laurencecrew/elead_dash/src/bitmaps.h

#ifndef BITMAPS_H
#define BITMAPS_H

#include <Arduino.h>

/*
	Bitmaps generated with http://javl.github.io/image2cpp/
*/

// 'icon_batt1', 6x11px
const unsigned char bm_icon_batt1 [] PROGMEM = {
	0x78, 0xfc, 0xfc, 0xcc, 0x8c, 0xcc, 0xcc, 0xcc, 0xcc, 0xfc, 0xfc
};
/* 'icon_batt2', 6x11px
const unsigned char bm_icon_batt2 [] PROGMEM = {
	0x78, 0xfc, 0xfc, 0x84, 0xb4, 0xe4, 0xcc, 0x9c, 0x84, 0xfc, 0xfc
};*/
// 'icon_motor', 6x11px
const unsigned char bm_icon_motor [] PROGMEM = {
	0x30, 0x30, 0x78, 0xfc, 0x00, 0xfc, 0xfc, 0xfc, 0xfc, 0xfc, 0x78
};
// 'warn_batt', 6x10px
const unsigned char bm_warn_batt [] PROGMEM = {
	0x78, 0xfc, 0xcc, 0xcc, 0xcc, 0xcc, 0xfc, 0xcc, 0xcc, 0xfc
};
// 'label_degrees', 15x9px
const unsigned char bm_label_degrees [] PROGMEM = {
	0x78, 0x7c, 0xcc, 0xfe, 0x85, 0xc6, 0x85, 0x80, 0xcd, 0x80, 0x79, 0x80, 0x01, 0xc6, 0x00, 0xfe, 
	0x00, 0x7c
};
// 'warn_cont', 6x10px
const unsigned char bm_warn_cont [] PROGMEM = {
	0xfc, 0xf8, 0xcc, 0xc8, 0xcc, 0xc8, 0xfc, 0xc8, 0xcc, 0xfc
};
// 'icon_cont', 6x11px
const unsigned char bm_icon_cont [] PROGMEM = {
	0xfc, 0xfc, 0xf8, 0xfc, 0xf8, 0xfc, 0xf8, 0xfc, 0xf8, 0xfc, 0xfc
};
// 'icon_sport', 37x13px
const unsigned char bm_icon_sport [] PROGMEM = {
	0x7f, 0xff, 0xff, 0xff, 0xf0, 0xff, 0xff, 0xff, 0xff, 0xf8, 0xf8, 0xc3, 0x8c, 0x30, 0x38, 0xf0, 
	0x41, 0x04, 0x10, 0x38, 0xf2, 0x49, 0x24, 0x9c, 0xf8, 0xf1, 0xc9, 0x24, 0x1c, 0xf8, 0xf8, 0xc1, 
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
	0x8a, 0x22, 0x88, 0x80
};
// 'icon_trip', 13x13px
const unsigned char bm_icon_trip [] PROGMEM = {
	0x0f, 0x80, 0x10, 0x40, 0x22, 0x20, 0x42, 0x10, 0x82, 0x08, 0x82, 0x08, 0x83, 0xc8, 0x80, 0x08, 
	0x80, 0x08, 0x40, 0x10, 0x20, 0x20, 0x10, 0x40, 0x0f, 0x80
};

#endif
